planckgabriel15-jpg/Proyect/Projects/VJN001/png/F1_bloques_y_lineas.png

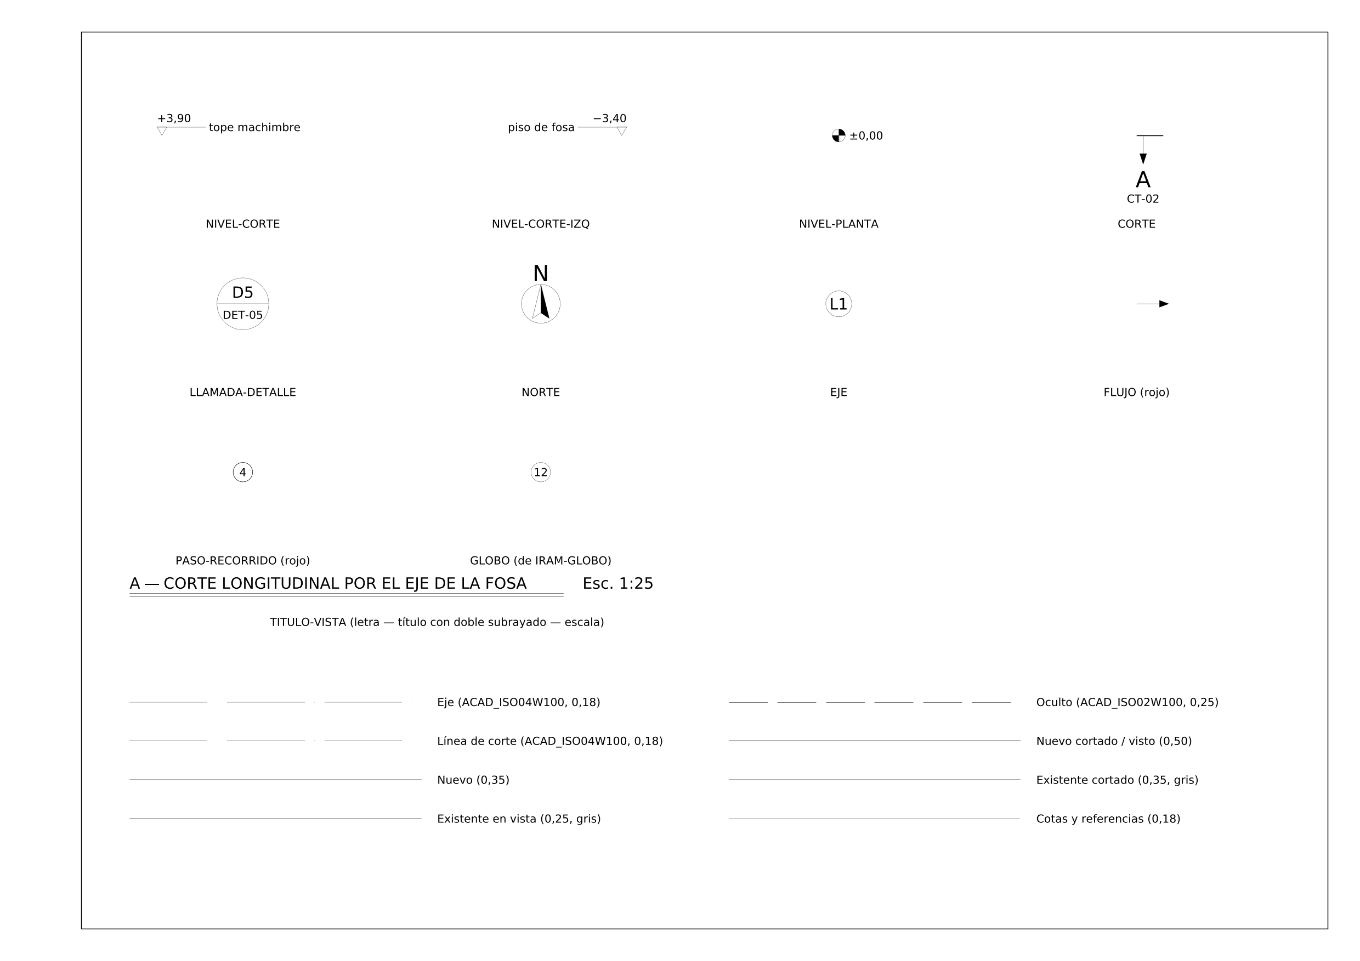
Projects/VJN001/png/F1_bloques_y_lineas.png
