planckgabriel15-jpg/Proyect/Projects/VJN001/png/F1_lamina_A3_muestra.png

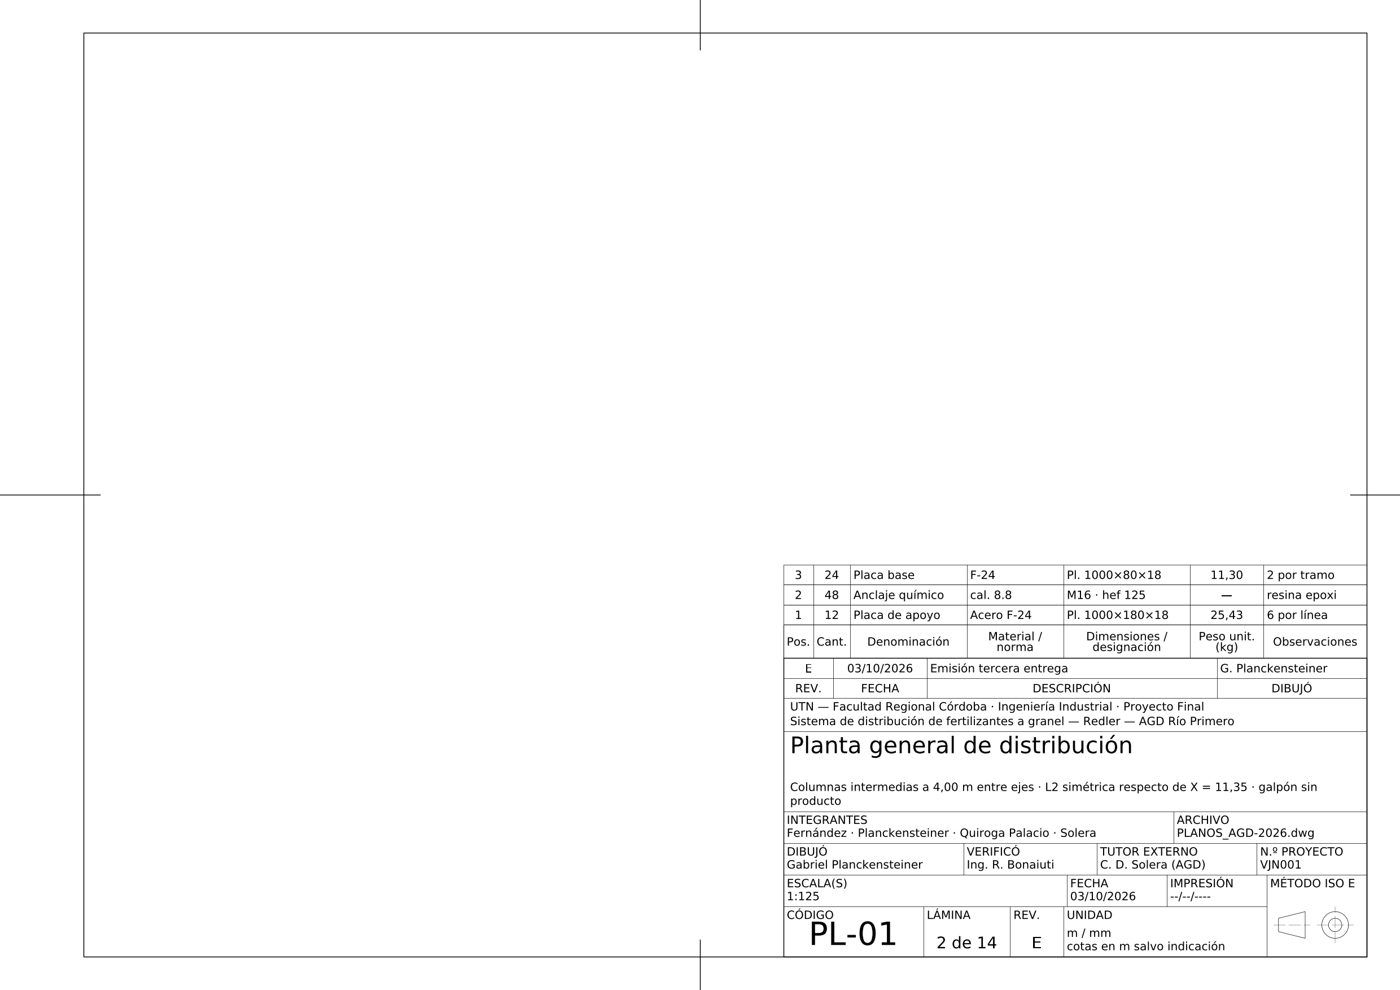
Projects/VJN001/png/F1_lamina_A3_muestra.png
