planckgabriel15-jpg/Proyect/Projects/VJN001/png/F2_A_corte_AA_1-75.png

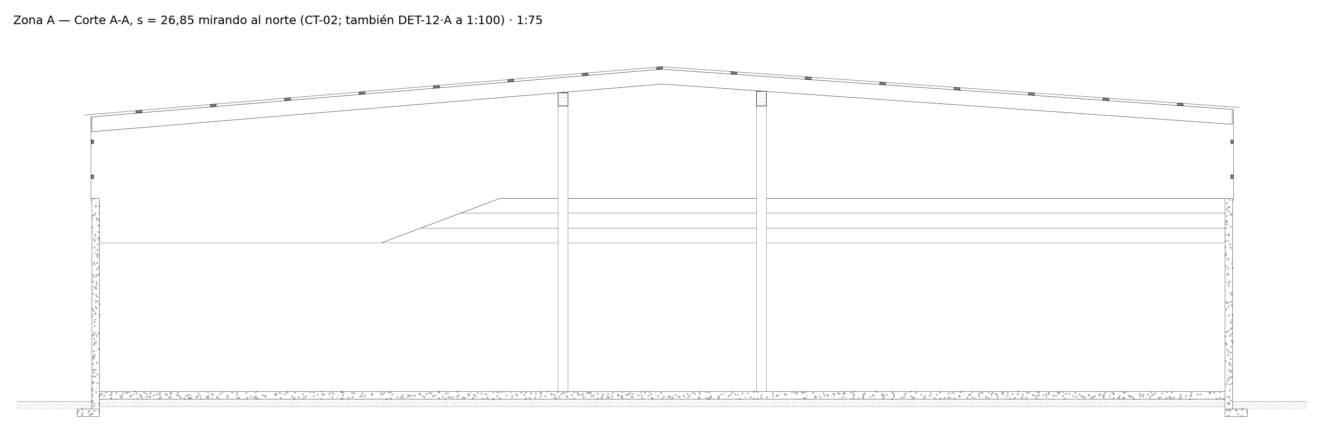
Projects/VJN001/png/F2_A_corte_AA_1-75.png
