planckgabriel15-jpg/Proyect/Projects/VJN001/png/F2_B_corte_BB_1-125.png

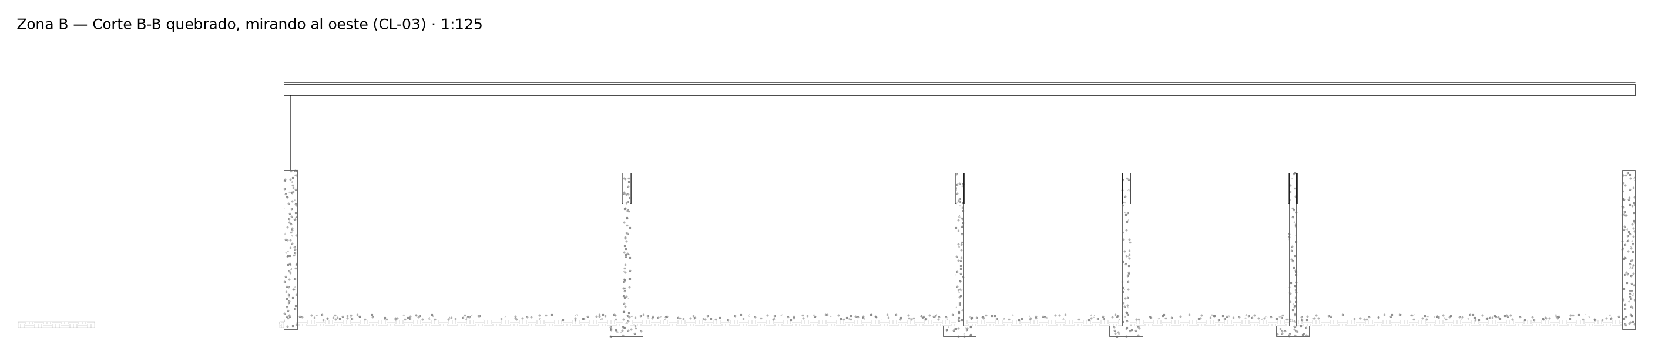
Projects/VJN001/png/F2_B_corte_BB_1-125.png
