planckgabriel15-jpg/Proyect/Projects/VJN001/png/F2_C_vista_CC_1-125.png

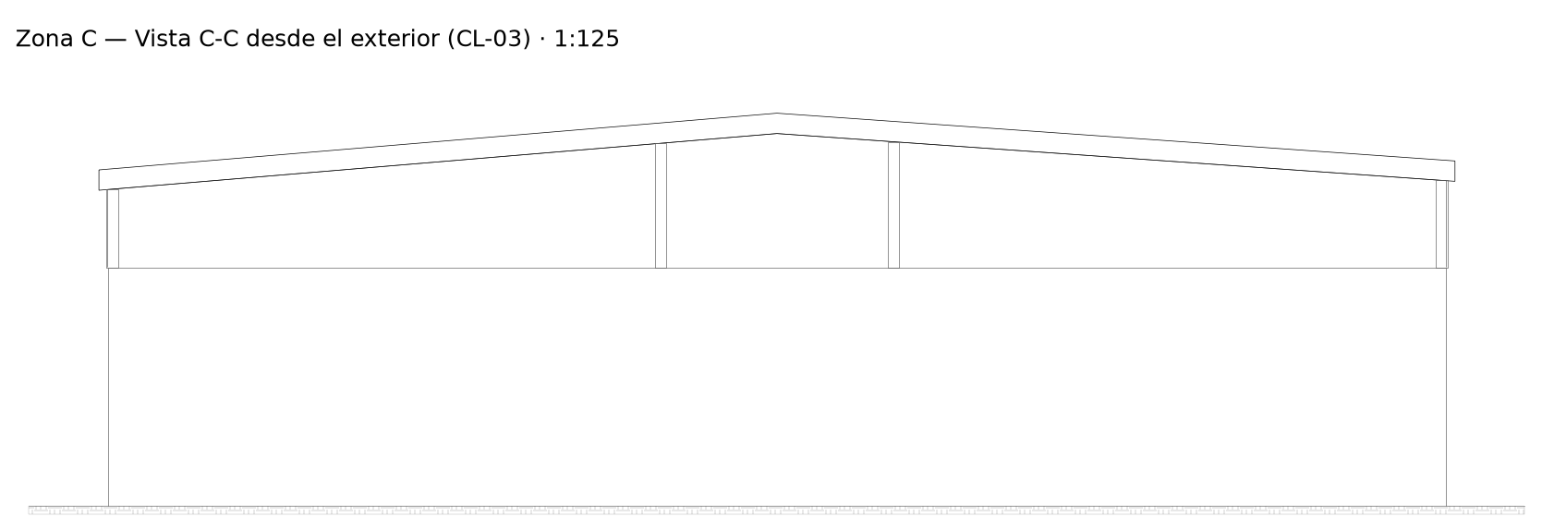
Projects/VJN001/png/F2_C_vista_CC_1-125.png
