planckgabriel15-jpg/Proyect/Projects/VJN001/png/F2_DET12_B_tabique_1-25.png

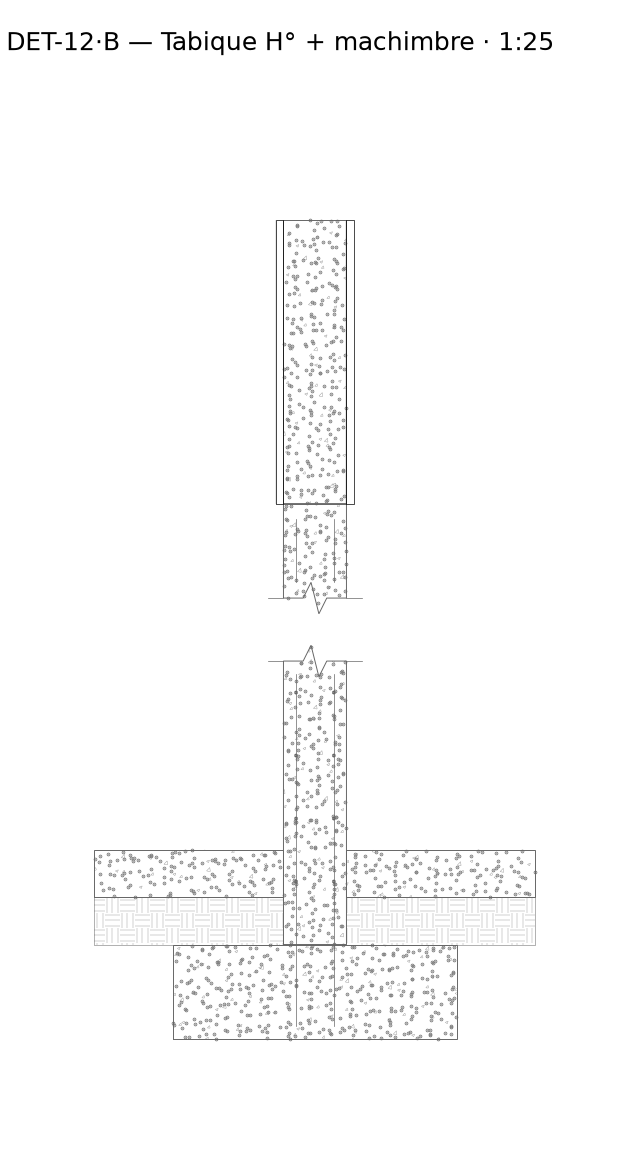
Projects/VJN001/png/F2_DET12_B_tabique_1-25.png
