planckgabriel15-jpg/Proyect/Projects/VJN001/png/F2_DET12_E_suplemento_1-200.png

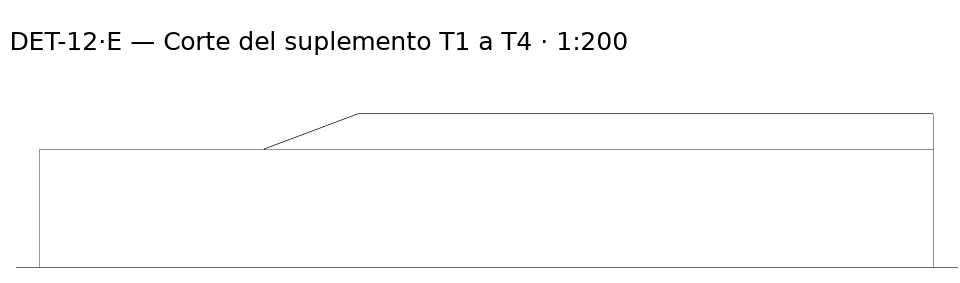
Projects/VJN001/png/F2_DET12_E_suplemento_1-200.png
