planckgabriel15-jpg/Proyect/Projects/VJN001/png/F2_DET12_F_dado_existente_1-20.png

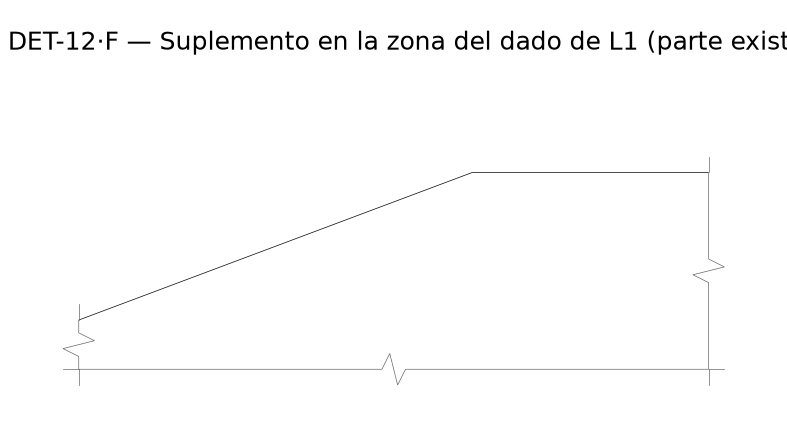
Projects/VJN001/png/F2_DET12_F_dado_existente_1-20.png
