planckgabriel15-jpg/Proyect/Projects/VJN001/png/F2_P_planta_1-125.png

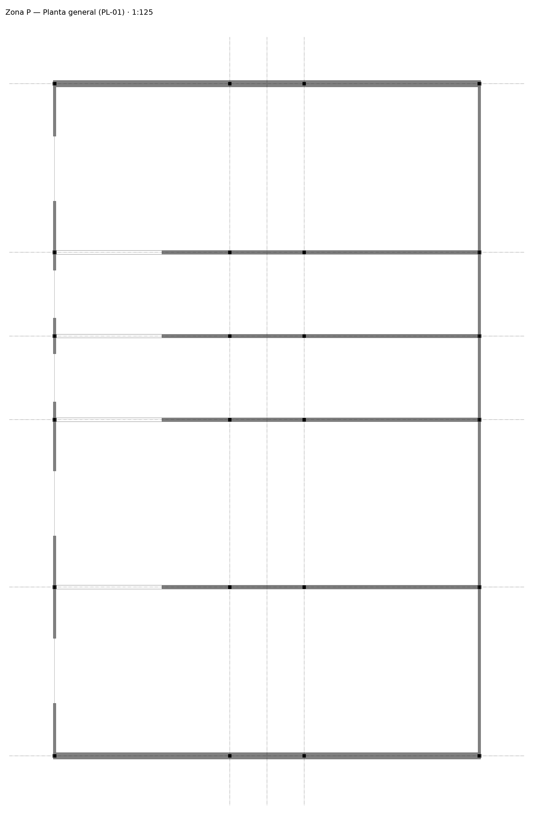
Projects/VJN001/png/F2_P_planta_1-125.png
